brucemack/microlink/docs/cad-1.jpg

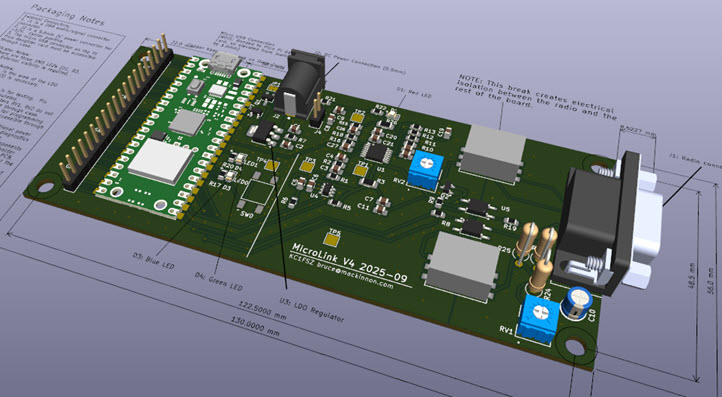
docs/cad-1.jpg
