brucemack/microlink/docs/demo-1.png

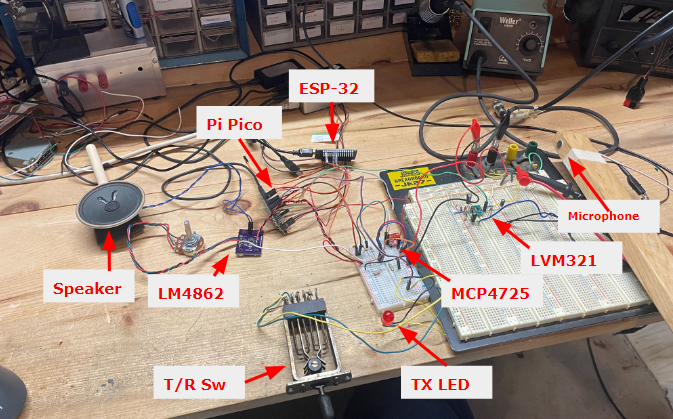
docs/demo-1.png
