brucemack/microlink/docs/preamp-2.png

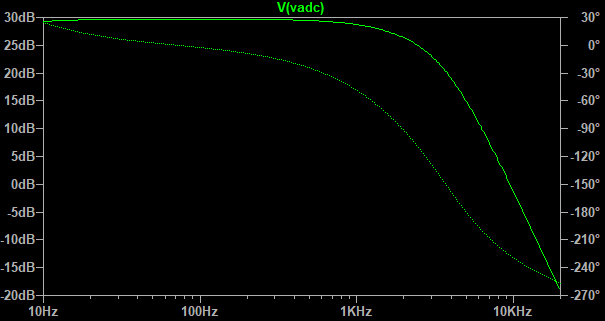
docs/preamp-2.png
