brucemack/microlink/docs/station-1.jpeg

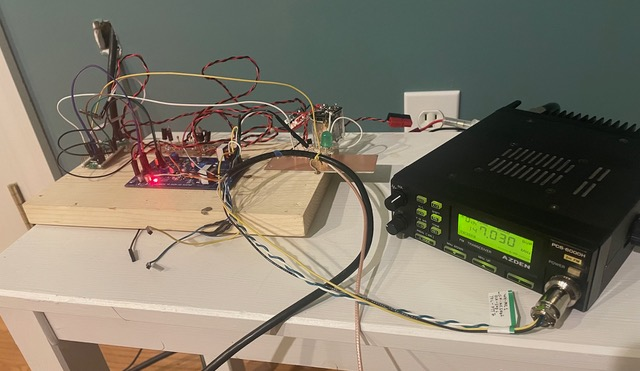
docs/station-1.jpeg
