brucemack/microlink/docs/tx-audio-2.PNG

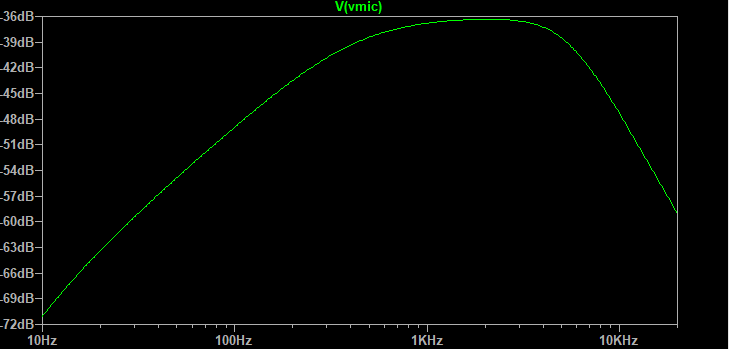
docs/tx-audio-2.PNG
