brucemack/microlink/docs/v0-board-0.jpeg

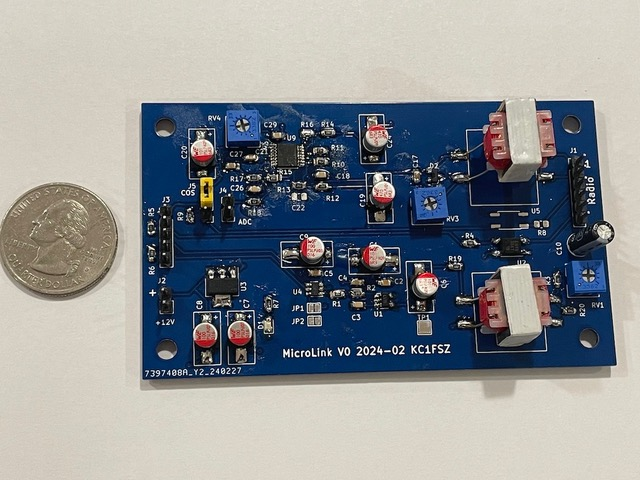
docs/v0-board-0.jpeg
