brucemack/microlink/docs/v1-board-0.jpeg

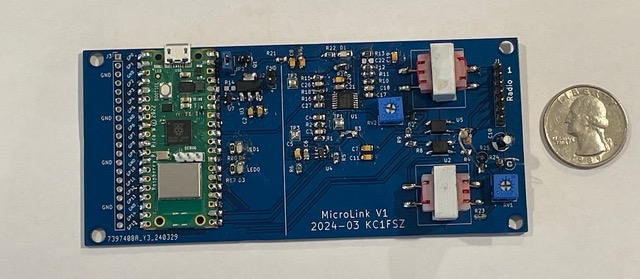
docs/v1-board-0.jpeg
