brucemack/microlink/docs/v3-station-0.jpeg

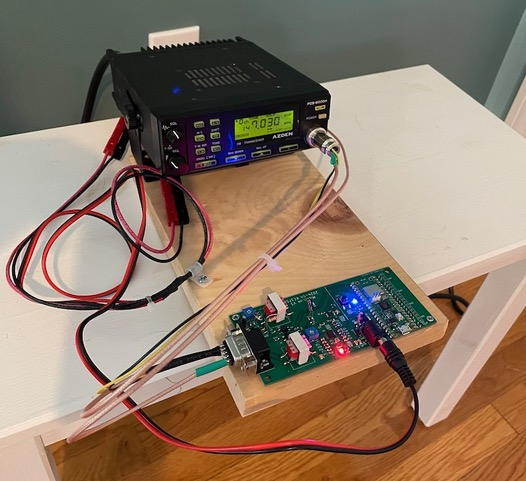
docs/v3-station-0.jpeg
