brucemack/microlink/hw/SA818-Breakout/docs/board-1.jpg

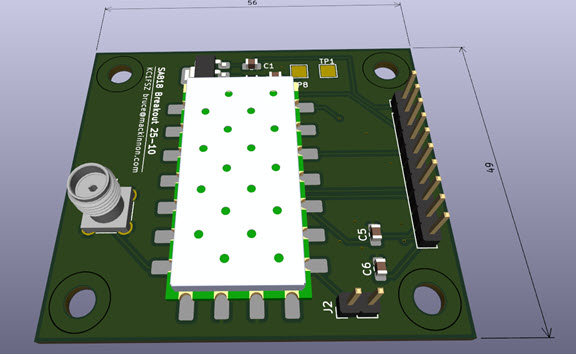
hw/SA818-Breakout/docs/board-1.jpg
