brucemack/microlink/hw/audio/PWM-Reconstruction-Filter.asc

C1: cap; 100n
C2: cap; 47µ
C3: cap; 100n
R1: res; 1k
R2: res; 220
R3: res; 1.8k
R4: res; 1k
V1: voltage; PULSE(0 3.3 0 0 0 {X} 15.6u); AC 1
Named nets: 0, Vout, Vin
.tran .001
.step param X list 1u 3u 5u 7u 9u 11u 13u 15u
