brucemack/microlink/hw/audio/tx-audio-1.asc

C1: polcap; 100µ
C2: polcap; 47µ
C4: cap; 10n
C5: cap; 22n
C6: polcap; 470µ
C8: polcap; 47µ
C10: cap; 0.1µ
C12: polcap; 47µ
L1: ind; 470µ
L2: ind2; 250m
L3: ind2; 250m
R1: res; 1k
R2: res; 1100
R3: res; 1k
R4: res; 1k
R5: res; 9k
R6: res; 1.5k
R7: res; 2.7k
R8: res; 600
U2: UniversalOpAmp
V1: voltage; 3.3
V2: voltage; SINE(1.6 1.6 1000); AC 1
Named nets: 0, Vmic, Vlpf
LPF for re-construction
Two poles, fc = 4 kHz
;tran 50m
.ac oct 100 100 4k
TLV9161
;.STEP param X list 220 470 1k 2k 5k 10k
MicroLink Transmit Audio
22-Feb-2024
Bruce MacKinnon KC1FSZ (improved by W1DAN)
MCP4725 DAC Output
(3.3 Vpp centered at 1.6V)
K1 L2 L3 1
R3/R5 potentiometer used 
to adjust gain of output 
(into rig microphone)
DC block cap for 
phantom power used to power
electret mics on some rigs
Rig ground in real circuit
(Add W2IHY 470uH/0.001uF 
RF block here)
600:600 Isolation 
Transformer 
(Estimated L=150mH)
Impedance of mic input of 
IC-2000H measured (approximately)
