brucemack/microlink/hw/audio/mic-preamp.asc

C1: cap; 100n
C2: polcap; 1µ
C3: polcap; 47µ
C4: cap; 10n
C5: cap; 22n
C6: polcap; 470µ
C7: polcap; 470µ
C8: polcap; 47µ
C10: cap; 0.1µ
C11: cap; 0.1µ
C12: polcap; 47µ
L1: ind; 470µ
R1: res; 2.2k
R2: res; 270k
R3: res; 270k
R4: res; 2.2k
R5: res; 170k
R6: res; 1.5k
R7: res; 2.7k
R8: res; 100k
U1: UniversalOpAmp
U2: UniversalOpAmp
V1: voltage; 3.3
V2: voltage; SINE(0 5m 1000); AC 1; Rser=2k
Named nets: 0, Vmic, Vadc
Electret Capsule Microphone
Bias resistor for microphone
(Measured bias voltage at mic
2.8V)
First stage adds 1.6V offset and provides
x75 voltage gain for microphone.
One pole of LPF at fc=4kHz
Second stage is a LPF for anti-aliasing.
Two poles, fc = 4 kHz
ADC on RP2040 has input impedance 
of 100k, per datasheet.
 
Goal is to have 3.3Vpp centered at 1.6V
to get full range of ADC.
;tran 50m
.ac oct 100 10 20k
LMV321
LMV321
.STEP param X list 300n 700n 1u 10u
MicroLink Microphone Pre-Amp
12-Feb-2024
Bruce MacKinnon KC1FSZ
With improvements from Dan Brown W1DAN
