brucemack/microlink/src/Prompts.cpp

/**
 * MicroLink EchoLink Station
 * Copyright (C) 2024, Bruce MacKinnon KC1FSZ
 *
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
 * FOR AMATEUR RADIO USE ONLY.
 * NOT FOR COMMERCIAL USE WITHOUT PERMISSION.
 */
#include <cstdint>
#include "Prompts.h"

namespace kc1fsz {

Sound SoundMeta[40] = {
{'A',0, 27}, 
{'B',27, 23}, 
{'C',50, 26}, 
{'D',76, 24}, 
{'E',100, 28}, 
{'F',128, 20}, 
{'G',148, 26}, 
{'H',174, 25}, 
{'I',199, 26}, 
{'J',225, 26}, 
{'K',251, 27}, 
{'L',278, 24}, 
{'M',302, 25}, 
{'N',327, 25}, 
{'O',352, 25}, 
{'P',377, 23}, 
{'Q',400, 26}, 
{'R',426, 28}, 
{'S',454, 20}, 
{'T',474, 23}, 
{'U',497, 24}, 
{'V',521, 26}, 
{'W',547, 28}, 
{'X',575, 23}, 
{'Y',598, 28}, 
{'Z',626, 28}, 
{'0',654, 31}, 
{'1',685, 26}, 
{'2',711, 26}, 
{'3',737, 28}, 
{'4',765, 25}, 
{'5',790, 26}, 
{'6',816, 24}, 
{'7',840, 30}, 
{'8',870, 25}, 
{'9',895, 31}, 
{'!',926, 35}, 
{'@',961, 29}, 
{'#',990, 47}, 
{'_',1037, 25}, 
};

static uint8_t SoundData[1062 * 33] = {
215, 166, 140, 37, 83, 80, 0, 188, 212, 146, 79, 156, 94, 161, 120, 229, 53, 185, 156, 128, 192, 184, 243, 205, 90, 172, 206, 128, 227, 183, 106, 72, 254, 
215, 164, 172, 93, 154, 225, 97, 71, 44, 145, 25, 92, 102, 193, 59, 43, 109, 203, 212, 184, 193, 91, 87, 114, 191, 27, 84, 192, 212, 44, 205, 86, 170, 
215, 167, 155, 170, 18, 196, 192, 246, 179, 142, 54, 249, 230, 129, 101, 101, 54, 204, 212, 104, 192, 185, 117, 90, 220, 116, 174, 160, 144, 85, 251, 228, 34, 
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
        if (SoundMeta[i].code == code) {
            return i;
        }
    }
    // Not found is '_' (silence)
    return 39;
}

void Sound::getGSMFrame(int f, uint8_t* gsmData) {
    for (unsigned int i = 0; i < 33; i++) {
        gsmData[i] = SoundData[((start + f) * 33) + i];
    }
}

}
