brucemack/microlink/src/contexts/LwIPLib.h

/**
 * MicroLink EchoLink Station
 * Copyright (C) 2024, Bruce MacKinnon KC1FSZ
 *
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
 * FOR AMATEUR RADIO USE ONLY.
 * NOT FOR COMMERCIAL USE WITHOUT PERMISSION.
 */
#ifndef _LwIPLib_h
#define _LwIPLib_h

#include "lwip/tcp.h"
#include "lwip/udp.h"

#include "kc1fsz-tools/Runnable.h"
#include "kc1fsz-tools/Channel.h"
#include "kc1fsz-tools/HostName.h"
#include "kc1fsz-tools/IPAddress.h"
#include "kc1fsz-tools/IPLib.h"

namespace kc1fsz {

class Log;

/**
 * IMPORTANT: We are assuming that this runs on an embedded processor
 * we so limit the use of C++ features.
 */
class LwIPLib : public IPLib, public Runnable {
public:

    static int traceLevel;

    LwIPLib(Log* log);

    // ----- Runnable Methods ------------------------------------------------

    /**
     * This should be called from the event loop.  It attempts to make forward
     * progress and passes all events to the event processor.
     * 
     * @returns true if any events were dispatched.
    */
    virtual void run();

    // ----- From IPLib ------------------------------------------------------

    virtual bool isLinkUp() const;

    virtual void addEventSink(IPLibEvents* e);

    virtual void queryDNS(HostName hostName);

    virtual Channel createTCPChannel();
    virtual void connectTCPChannel(Channel c, IPAddress ipAddr, uint32_t port);
    virtual void sendTCPChannel(Channel c, const uint8_t* b, uint16_t len);

    virtual Channel createUDPChannel();
    virtual void bindUDPChannel(Channel c, uint32_t port);
    virtual void sendUDPChannel(const Channel& c, 
        const IPAddress& remoteIpAddr, uint32_t remotePort,
        const uint8_t* b, uint16_t len);

    virtual void closeChannel(Channel c);

private:

    Log* _log;

    static const uint32_t _maxEvents = 16;
    IPLibEvents* _events[_maxEvents];
    uint32_t _eventsLen = 0;
    
    bool _inCallback = false;

    HostName _lastHostNameReq;
    IPAddress _lastAddrResp;
    Channel _lastChannel;

    // At the moment we can have at most one DNS request outstanding
    // at a time.
    bool _dnsRespPending = false;

    // At the moment we can have at most two bind requests outstanding
    // at a time.    
    static const uint32_t _bindRespQueueSize = 4;
    Channel _bindRespQueue[_bindRespQueueSize];
    uint32_t _bindRespQueueLen = 0;

    static const uint32_t _sendHoldSize = 256;
    uint8_t _sendHold[_sendHoldSize];
    uint32_t _sendHoldLen;

    bool _resetPending = false;

    struct Tracker {

        bool inUse = false;
        bool error = false;

        enum Type {
            NONE, 
            TCP,
            UDP
        } type = Type::NONE;

        enum State {
            IDLE,
            IN_CONNECT
        } state = State::IDLE;

        void* pcb = 0;
    };

    static const uint32_t _trackersSize = 6;
    Tracker _trackers[_trackersSize];
   
    void _validateChannel(const Channel& c, Tracker::Type t) const;
    Tracker* _findTracker(void* tpcb);
    int _findTracker2(void* tpcb);

    static err_t _tcpRecvCb(void *arg, tcp_pcb *tpcb, pbuf *p, err_t err);
    err_t _tcpRecv(tcp_pcb *tpcb, pbuf *p, err_t err);

    static err_t _tcpSentCb(void *arg, tcp_pcb *tpcb, u16_t len);

    static err_t _tcpConnectCb(void *arg, tcp_pcb *tpcb, err_t err);
    err_t _tcpConnect(tcp_pcb *tpcb, err_t err);

    static void _udpRecvCb(void *arg, udp_pcb *upcb, pbuf *p, const ip_addr_t *addr, u16_t port);
    void _udpRecv(udp_pcb *upcb, pbuf *p, const ip_addr_t *addr, u16_t port);

    static void _errCb(void *arg, err_t err);

    static void _dnsCb(const char* name, const ip_addr_t* ipaddr, void *callback_arg);
    void _dns(const char* name, const ip_addr_t* ipaddr);

    void _dumpChannels() const;
};

}

#endif
