brucemack/microlink/tests/client-test-2.cpp

/**
 * MicroLink EchoLink Station
 * Copyright (C) 2024, Bruce MacKinnon KC1FSZ
 *
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
 * FOR AMATEUR RADIO USE ONLY.
 * NOT FOR COMMERCIAL USE WITHOUT PERMISSION.
 * 
 * =================================================================================
 * This file is unit-test code only.  None of this should be use for 
 * real applications!
 * =================================================================================
 * 
 * This test case is targeted at the Windows platform. This is a basic EL client.
 */
#include <fcntl.h>

#include <iostream>
#include <fstream>
#include <cassert>
#include <cstring>
#include <string>
#include <thread>
#include <chrono>

#include "kc1fsz-tools/events/TickEvent.h"
#include "kc1fsz-tools/win32/Win32PerfTimer.h"
//#include "kc1fsz-tools/win32/Win32PollTimer.h"

#include "machines/RootMachine.h"
#include "contexts/SocketContext.h"
#include "contexts/W32AudioOutputContext.h"

#include "TestUserInfo.h"
#include "TestAudioInputContext.h"

using namespace std;
using namespace kc1fsz;

// The size of one EchoLink RTP packet (after decoding)
static const int audioFrameSize = 160 * 4;
static const int audioFrameCount = 16;
// Double-buffer
static int16_t audioFrameOut[audioFrameCount * audioFrameSize];
// Double-buffer
static int16_t silenceFrameOut[2 * audioFrameSize];

int main(int, const char**) {

    cout << "===== MicroLink Test 2 ==================" << endl;
    cout << "Copyright (C) 2024 Bruce MacKinnon KC1FSZ" << endl;

    RootMachine::traceLevel = 0;
    LogonMachine::traceLevel = 0;
    LookupMachine2::traceLevel = 0;
    QSOConnectMachine::traceLevel = 1;
    QSOFlowMachine::traceLevel = 1;
    SocketContext::traceLevel = 0;
    W32AudioOutputContext::traceLevel = 1;

    if (getenv("EL_CALLSIGN") == 0 || getenv("EL_PASSWORD") == 0 ||
        getenv("EL_FULLNAME") == 0 || getenv("EL_LOCATION") == 0) {
        cout << "EL_CALLSIGN, EL_PASSWORD, EL_FULLNAME, EL_LOCATION must be set." << endl;
        return -1;
    }

    SocketContext context;
    TestUserInfo info;
    W32AudioOutputContext audioOutContext(audioFrameSize, 8000, audioFrameOut, silenceFrameOut);
    TestAudioInputContext audioInContext(audioFrameSize, 8000);

    RootMachine rm(&context, &info, &audioOutContext);
    rm.setServerName(HostName("naeast.echolink.org"));
    rm.setServerPort(5200);
    rm.setCallSign(CallSign(getenv("EL_CALLSIGN")));
    rm.setPassword(FixedString(getenv("EL_PASSWORD")));
    rm.setFullName(FixedString(getenv("EL_FULLNAME")));
    rm.setLocation(FixedString(getenv("EL_LOCATION")));
    rm.setTargetCallSign(CallSign("*ECHOTEST*"));

    context.setEventProcessor(&rm);
    // Send input audio into station transmit port
    audioInContext.setSink(&rm);

    TickEvent tickEv;
    uint32_t lastAudioTickMs = 0;

    Win32PerfTimer socketTimer;
    uint32_t longestSocketUs = 0;

    //Win32PollTimer slowTimer;
    //slowTimer.setIntervalUs(1000000);

    uint32_t cycle = 0;

    // Make stdin non-blocking so that getchar() doesn't hang
    fcntl(0, F_SETFL, O_NONBLOCK); 

    // Here is the main event loop
    while (true) {

        int c = getchar();
        if (c == 'q') {
            cout << "Leaving event loop" << endl;
            break;
        }
        else if (c == 't') {
            cout << "Transmit tone" << endl;  
            // Short burst of tone
            audioInContext.sendTone(1000, 1000);
        } 
        else if (c == 's') {
            cout << "Starting" << endl;
            rm.start();
        }

        bool activity = false;

        // Poll the audio input system at full speed
        activity = activity || audioInContext.poll();

        // Poll the audio output system at full speed
        activity = activity || audioOutContext.poll();

        // Poll the communications system at full speed
        socketTimer.reset();
        activity = activity || context.poll();
        uint32_t ela = socketTimer.elapsedUs();
        if (ela > longestSocketUs) {
            longestSocketUs = ela;
            cout << "Longest Socket " << longestSocketUs << endl;
        
        }

        // Generate a clock every second for timeouts, etc.
        uint32_t now = time_ms();
        if (now - lastAudioTickMs >= 1000) {
            lastAudioTickMs = now;
            rm.processEvent(&tickEv);
        }

        // This is here only to avoid high-CPU loops
        // Tell the context to move forward
        //uint32_t t0 = time_ms();
        //std::this_thread::sleep_for(std::chrono::microseconds(500));
        std::this_thread::yield();
 
        if (!activity)
            Sleep(5);

        cycle++;
    }
}
