brucemack/microlink/tests/common-test-1.cpp

/**
 * MicroLink EchoLink Station
 * Copyright (C) 2024, Bruce MacKinnon KC1FSZ
 *
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
 * FOR AMATEUR RADIO USE ONLY.
 * NOT FOR COMMERCIAL USE WITHOUT PERMISSION.
 * 
 * =================================================================================
 * This file is unit-test code only.  None of this should be use for 
 * real applications!
 * =================================================================================
 */
#include <fcntl.h>
#include <sys/socket.h>
#include <unistd.h>

#include "Windows.h"

#include <iostream>
#include <fstream>
#include <cassert>
#include <cstring>
#include <string>

#include "kc1fsz-tools/Common.h"
#include "kc1fsz-tools/win32/Win32PerfTimer.h"
#include "common.h"

using namespace std;
using namespace kc1fsz;

static void test_stdin() {

    int rc = fcntl(0, F_SETFL, O_NONBLOCK); 
    cout << rc << endl;

    // Select on STDIN
    //fd_set readfds; 
    //FD_ZERO(&readfds);
    //int highestFd = 0;

    //struct timeval tv;
    //tv.tv_sec = 0;
    //tv.tv_usec = 100;

    //FD_SET(0, &readfds);

    for (int i = 0; i < 100000; i++) {
        // Do the real thing
        //int rv = select(highestFd + 1, &readfds, 0, 0, &tv); 
        //if (rv != 0)
        //    cout << rv << endl;
        int c = getchar();
        if (c != -1)
            cout << c << endl;
    }
}

static void test_ip_addr() {
    uint32_t addr = parseIP4Address("1.2.3.4");
    char buf[64];
    formatIP4Address(addr, buf, 64);
    assert(strcmp(buf, "1.2.3.4") == 0);
}

static void test_print() {
    uint8_t test[20] = { 0, 1, 2, 3, 4, 65, 6, 7, 8, 9, 10, 11, 12, 13, 
        48, 15, 16, 17, 18, 19 };
    prettyHexDump(test, 20, cout);
}

static void test_timing() {
#ifdef __CYGWIN__
    LARGE_INTEGER freq;
    QueryPerformanceFrequency(&freq); 

    // Notice here that it is difficult to sleep for only 5ms on Windows
    {
        LARGE_INTEGER pc0;
        QueryPerformanceCounter(&pc0);

        Sleep(5);

        LARGE_INTEGER pc1;
        QueryPerformanceCounter(&pc1);

        cout << "Elapsed Ticks " << pc1.QuadPart - pc0.QuadPart << endl;
        cout << "Elapsed uS    " << (pc1.QuadPart - pc0.QuadPart) * 1000000 / freq.QuadPart << endl;
    }

    // Put sleeping for 50ms is possible
    {
        LARGE_INTEGER pc0;
        QueryPerformanceCounter(&pc0);

        Sleep(50);

        LARGE_INTEGER pc1;
        QueryPerformanceCounter(&pc1);

        cout << "Elapsed Ticks " << pc1.QuadPart - pc0.QuadPart << endl;
        cout << "Elapsed uS    " << (pc1.QuadPart - pc0.QuadPart) * 1000000 / freq.QuadPart << endl;
    }
#endif

    // Test the timer class
    Win32PerfTimer timer;
    Sleep(50);
    cout << "Elapsed uS    " << timer.elapsedUs() << endl;
}

int main(int, const char**) {
    test_print();
    test_ip_addr();
    test_timing();
    test_stdin();
}
