brucemack/microlink/tests/audio-test-1.cpp

/**
 * MicroLink EchoLink Station
 * Copyright (C) 2024, Bruce MacKinnon KC1FSZ
 *
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
 * FOR AMATEUR RADIO USE ONLY.
 * NOT FOR COMMERCIAL USE WITHOUT PERMISSION.
 * 
 * =================================================================================
 * This file is unit-test code only.  None of this should be use for 
 * real applications!
 * =================================================================================
 */
#include <Windows.h>

#include <cstdint>
#include <iostream>
#include <cassert>
#include <cstring>
#include <cmath>

using namespace std;

// The size of one EchoLink RTP packet (after decoding)
const int NUMPTS = 160 * 4;
// Double-buffer
int16_t waveData[2][NUMPTS];

// A simple example of playing an audio tone using alternating buffers.
//
// For API details see:
// https://learn.microsoft.com/en-us/windows/win32/api/mmeapi/nf-mmeapi-waveoutopen
//
int main(int, const char**) {

    // Get the number of Digital Audio Out devices in this computer 
    // and display information about all of them.
    unsigned long iNumDevs = waveOutGetNumDevs();
    for (uint32_t i = 0; i < iNumDevs; i++) {
        WAVEOUTCAPS woc;
        if (!waveOutGetDevCaps(i, &woc, sizeof(WAVEOUTCAPS))) {
            printf("Device ID #%u: %s\r\n", i, woc.szPname);
        }
    }

    MMRESULT result;

    // Specify audio parameters
    int sampleRate = 8000;
    WAVEFORMATEX pFormat;
    pFormat.wFormatTag = WAVE_FORMAT_PCM;
    pFormat.nChannels = 1;
    pFormat.nSamplesPerSec = sampleRate;
    pFormat.nAvgBytesPerSec = sampleRate * 2;
    pFormat.nBlockAlign = 2;
    pFormat.wBitsPerSample = 16;
    pFormat.cbSize = 0;

    // Create an event that will be fired by the Wave system when it is 
    // ready to receive some more data.
    HANDLE event = CreateEvent( 
        NULL,               // default security attributes
        FALSE,              // TRUE=manual-reset event, FALSE=auto-reset
        FALSE,              // initial state is non-signaled
        TEXT("Done")        // object name
    ); 
    if (event == 0) {
        cout << "Event failed" << endl;
        return -1;
    }

    // Open the output channel - using the default output device (WAVE_MAPPER)
    HWAVEOUT waveOut;
    result = waveOutOpen(&waveOut, WAVE_MAPPER, &pFormat, (DWORD_PTR)event, 0L, 
        (WAVE_FORMAT_DIRECT | CALLBACK_EVENT));
    if (result) {
        cout << "Open failed" << endl;
        return -1;
    }

    // Set up and prepare buffers/headers for output.  We use to buffers
    // in alternating sequence. 
    WAVEHDR waveHdr[2];

    waveHdr[0].lpData = (LPSTR)waveData[0];
    waveHdr[0].dwBufferLength = NUMPTS * 2;
    waveHdr[0].dwBytesRecorded = 0;
    waveHdr[0].dwUser = 0L;
    waveHdr[0].dwFlags = 0L;
    waveHdr[0].dwLoops = 0L;
    result = waveOutPrepareHeader(waveOut, &(waveHdr[0]), sizeof(WAVEHDR));    
    if (result) {
        cout << "Prepare 0 failed" << endl;
        return -1;
    }

    waveHdr[1].lpData = (LPSTR)waveData[1];
    waveHdr[1].dwBufferLength = NUMPTS * 2;
    waveHdr[1].dwBytesRecorded = 0;
    waveHdr[1].dwUser = 0L;
    waveHdr[1].dwFlags = 0L;
    waveHdr[1].dwLoops = 0L;
    result = waveOutPrepareHeader(waveOut, &(waveHdr[1]), sizeof(WAVEHDR));    
    if (result) {
        cout << "Prepare 1 failed" << endl;
        return -1;
    }

    // Fill buffers with a consistent tone.  Normally this would be done
    // on-the-fly as audio arrives.  But we are pre-loading two buffers 
    // in a phase-continuous way to listen carefully for glitches.
    float freqRad = 1000.0 * 2.0 * 3.1415926;
    float omega = freqRad / (float)sampleRate;
    float phi = 0;
    for (int b = 0; b < 2; b++) {
        for (int i = 0; i < NUMPTS; i++) {
            waveData[b][i] = 32767.0 * std::cos(phi);
            phi += omega;
        }
    }

    int bufferCount = 0;
    int nextBuffer = bufferCount % 2;
    
    // Get things going by launching the first buffer
    result = waveOutWrite(waveOut, &(waveHdr[nextBuffer]), sizeof(WAVEHDR));
    if (result) {
        cout << "Write 0 failed" << endl;
        return -1;
    }

    // The test runs for some fixed period.  This is basically the main
    // event loop of the program.
    for (int i = 0; i < 200; i++) {

        // Check the status of the event (and un-signal it atomically if it is set)
        // Timeout is zero
        DWORD r = ::WaitForSingleObject(event, 0);
        if (r == 0) {

            bufferCount++;
            nextBuffer = bufferCount % 2;

            // Serve up the "other" buffer in alternating sequence
            result = waveOutWrite(waveOut, &(waveHdr[nextBuffer]), sizeof(WAVEHDR));
            if (result) {
                cout << "Write failed" << endl;
                return -1;
            }
        }
        else {
            cout << "Tick " << i << endl;
            // Theoretically the buffer size (160 * 4) is the same as 20ms of audio 
            // at 8,000.  So setting the sleep at 19 should be good enough to keep
            // the tone continuous.
            //
            // Try changing it to 50ms to see what I mean.
            Sleep(20);
        }
    }

    waveOutClose(waveOut);
    CloseHandle(event);
}
