brucemack/microlink/tests/TestUserInfo.h

#ifndef _TestUserInfo_h
#define _TestUserInfo_h

#include <iostream>

#include "kc1fsz-tools/Common.h"
#include "kc1fsz-tools/AudioOutputContext.h"

#include "../src/common.h"
#include "../src/UserInfo.h"

namespace kc1fsz {

class TestUserInfo : public UserInfo {
public:

    void setAudioOut(AudioOutputContext* o) { _audioOutCtx = o; }

    virtual void setStatus(const char* msg) { 
        std::cout << "UserInfo(Status): " << msg << std::endl; 
    }
    virtual void setOnData(const char* msg) { 
        std::cout << "UserInfo(oNDATA): [" << msg << "]" << std::endl; 
    }

    virtual void setSquelchOpen(bool sq) { 

        bool unkey = _squelch == true && sq == false;

        _squelch = sq;

        //std:: cout << "UserInfo: Squelch: " << _squelch << std::endl;

        // Short beep on unkey
        //if (unkey) {
        //    if (_audioOutCtx != 0) {
        //        _audioOutCtx->tone(400, 75);
        //    }
        //}

        if (unkey) {
            _lastSquelchCloseTime = time_ms();
        }
    }

    bool getSquelch() const { return _squelch; }
    
    uint32_t getMsSinceLastSquelchClose() const { 
        return ms_since(_lastSquelchCloseTime); 
    }

private:

    bool _squelch = false;
    AudioOutputContext* _audioOutCtx = 0;
    timestamp _lastSquelchCloseTime;
};

}

#endif
